RodrigoChe/fonte_de_bancada/cad_mecanico/COMPONENTES/sapata.SLDPRT

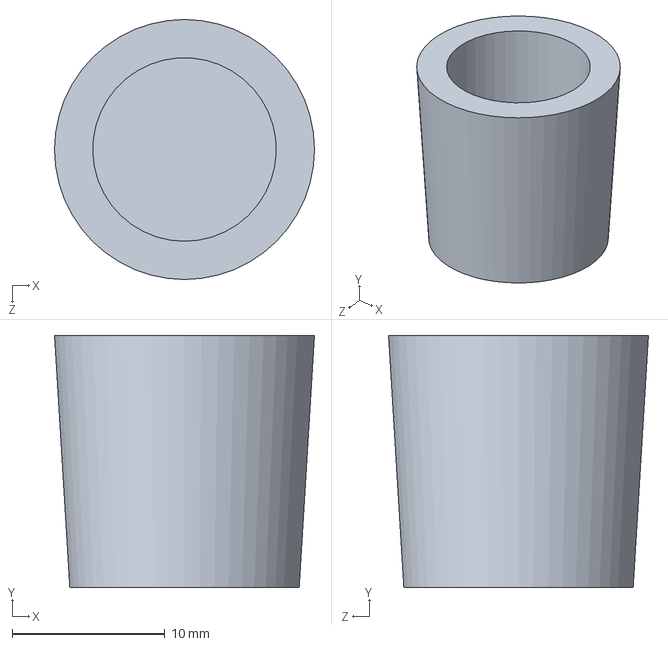
[picture p17: CAD file, 2024-03-11]
cad_mecanico/COMPONENTES/sapata.SLDPRT
17.0 x 16.5 x 17.0 mm
