RodrigoChe/fonte_de_bancada/cad_mecanico/COMPONENTES/trafo 3A.SLDPRT

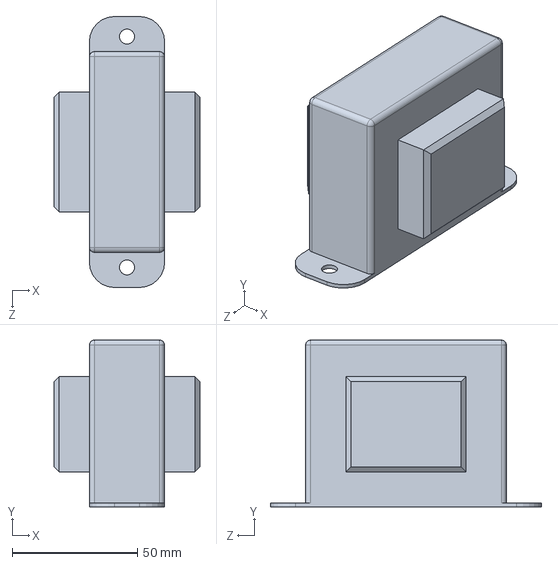
[picture p18: CAD file, 2024-03-11]
cad_mecanico/COMPONENTES/trafo 3A.SLDPRT
58.0 x 66.5 x 108.0 mm
