RodrigoChe/fonte_de_bancada/cad_mecanico/COMPONENTES/Chave HH.SLDPRT

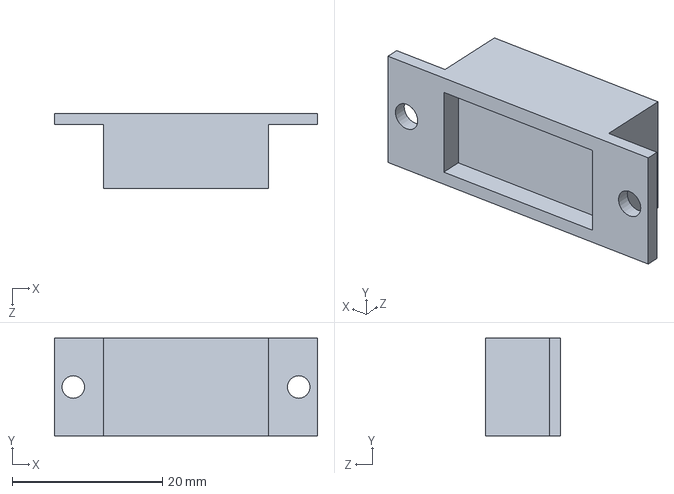
[picture p19: CAD file, 2024-03-11]
cad_mecanico/COMPONENTES/Chave HH.SLDPRT
35.0 x 13.0 x 10.0 mm
