RodrigoChe/fonte_de_bancada/cad_mecanico/COMPONENTES/Orelha.SLDPRT

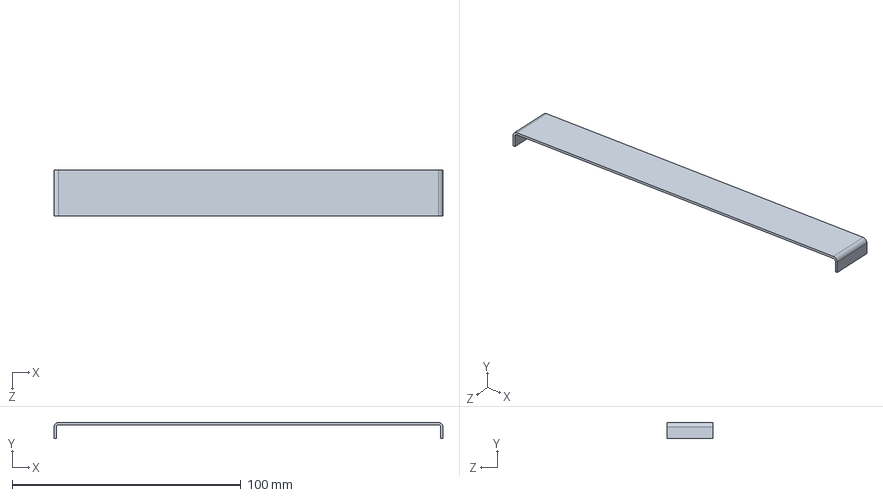
[picture p20: CAD file, 2024-03-11]
cad_mecanico/COMPONENTES/Orelha.SLDPRT
170.0 x 7.00 x 20.0 mm
