RodrigoChe/fonte_de_bancada/cad_mecanico/COMPONENTES/Frontal.SLDPRT

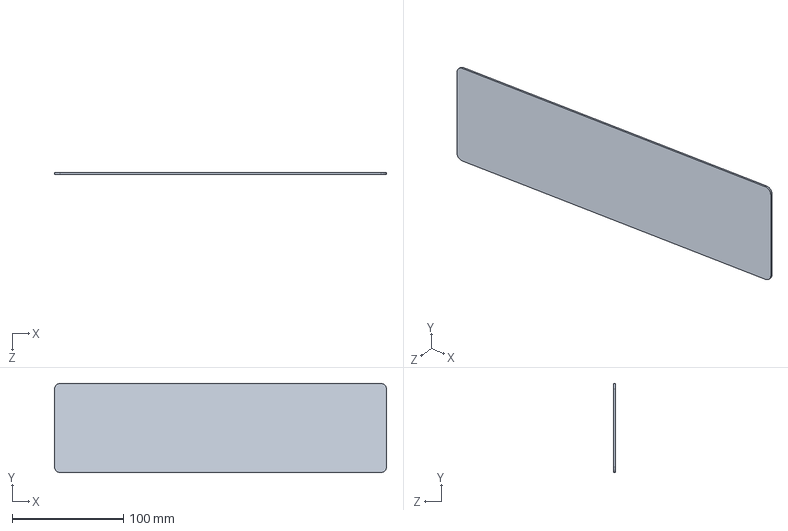
[picture p21: CAD file, 2024-03-11]
cad_mecanico/COMPONENTES/Frontal.SLDPRT
298.0 x 80.0 x 1.50 mm
