RodrigoChe/fonte_de_bancada/cad_mecanico/COMPONENTES/led holder.SLDPRT

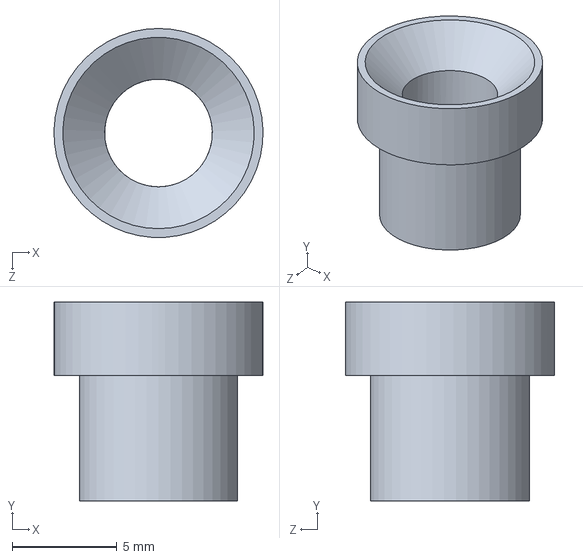
[picture p22: CAD file, 2024-03-11]
cad_mecanico/COMPONENTES/led holder.SLDPRT
9.99 x 9.50 x 10.0 mm
