RodrigoChe/fonte_de_bancada/prints_fotos_videos/cad_vista_monategm_1.png

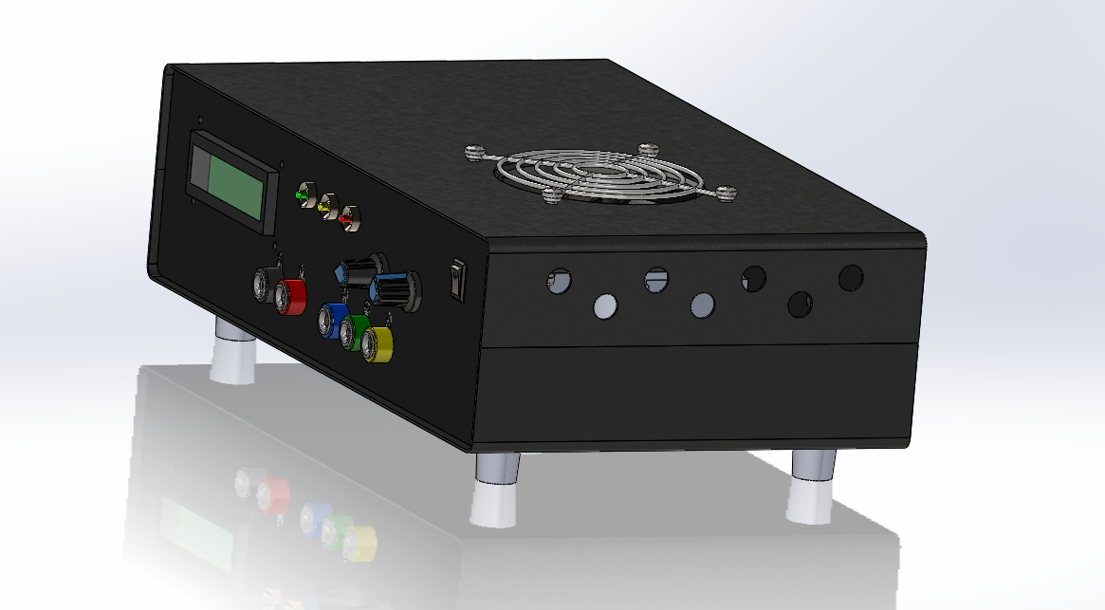
prints_fotos_videos/cad_vista_monategm_1.png
