RodrigoChe/fonte_de_bancada/prints_fotos_videos/cad_vista_monategm_2.png

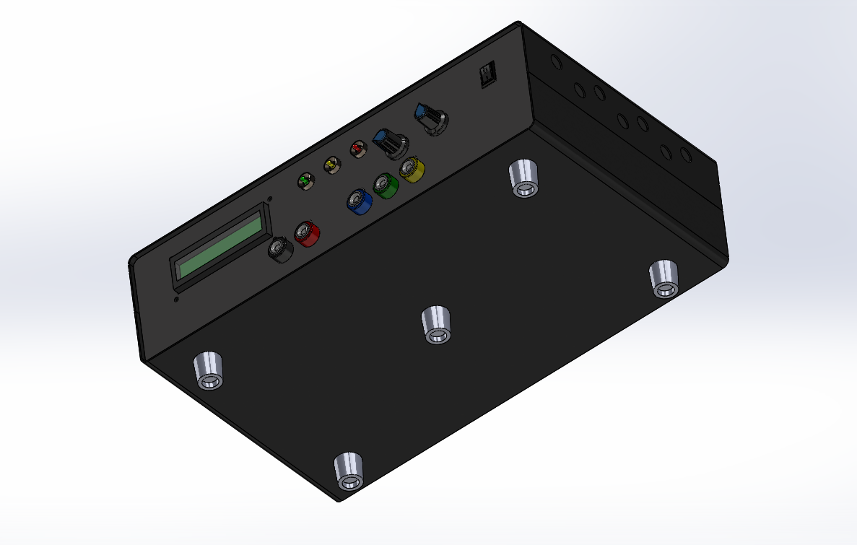
prints_fotos_videos/cad_vista_monategm_2.png
