RodrigoChe/fonte_de_bancada/prints_fotos_videos/IMG-20220224-WA0000.jpg

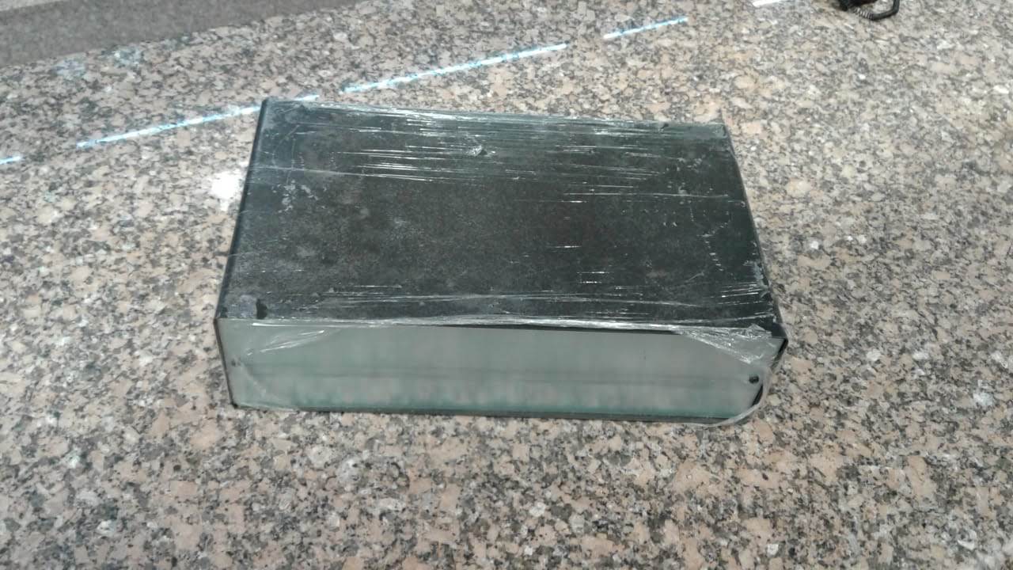
prints_fotos_videos/IMG-20220224-WA0000.jpg
