RodrigoChe/fonte_de_bancada/prints_fotos_videos/IMG-20240229-WA0002.jpeg

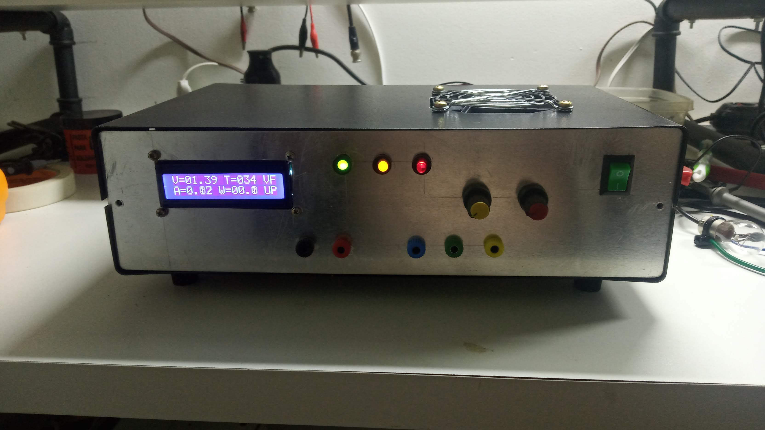
prints_fotos_videos/IMG-20240229-WA0002.jpeg
