RodrigoChe/fonte_de_bancada/prints_fotos_videos/IMG-20240301-WA0006.jpeg

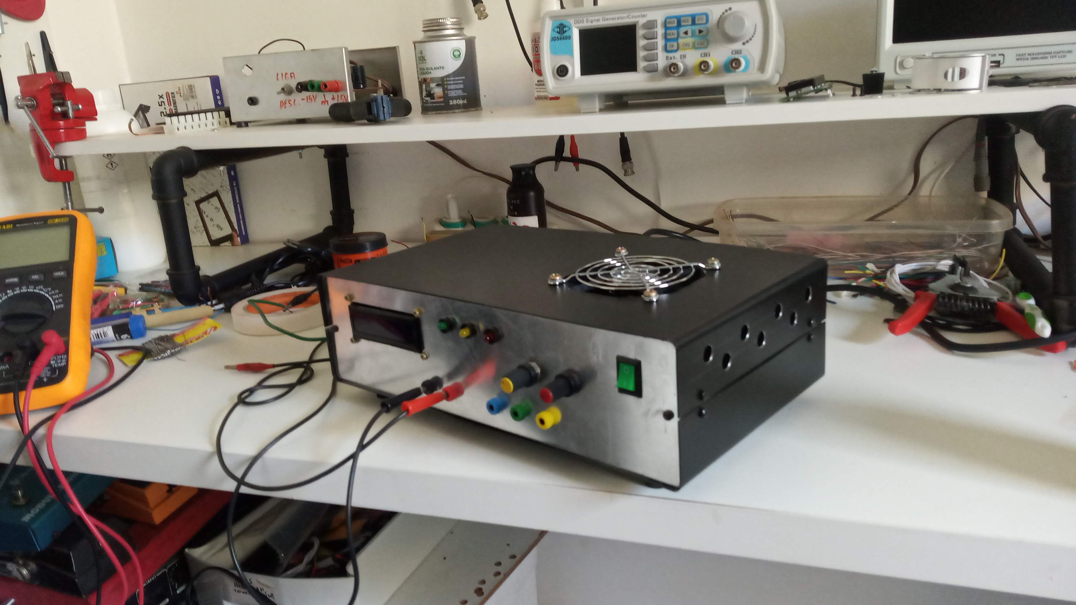
prints_fotos_videos/IMG-20240301-WA0006.jpeg
