RodrigoChe/fonte_de_bancada/prints_fotos_videos/IMG_20220310_143831.jpg

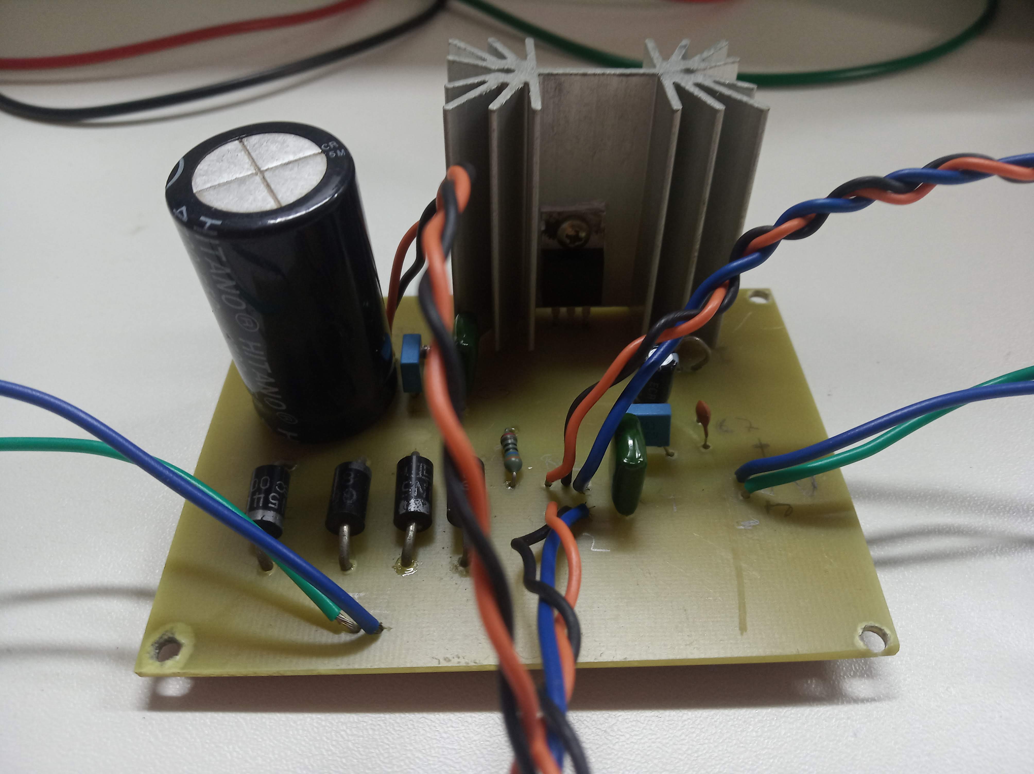
prints_fotos_videos/IMG_20220310_143831.jpg
