RodrigoChe/fonte_de_bancada/prints_fotos_videos/IMG_20220315_130520.jpg

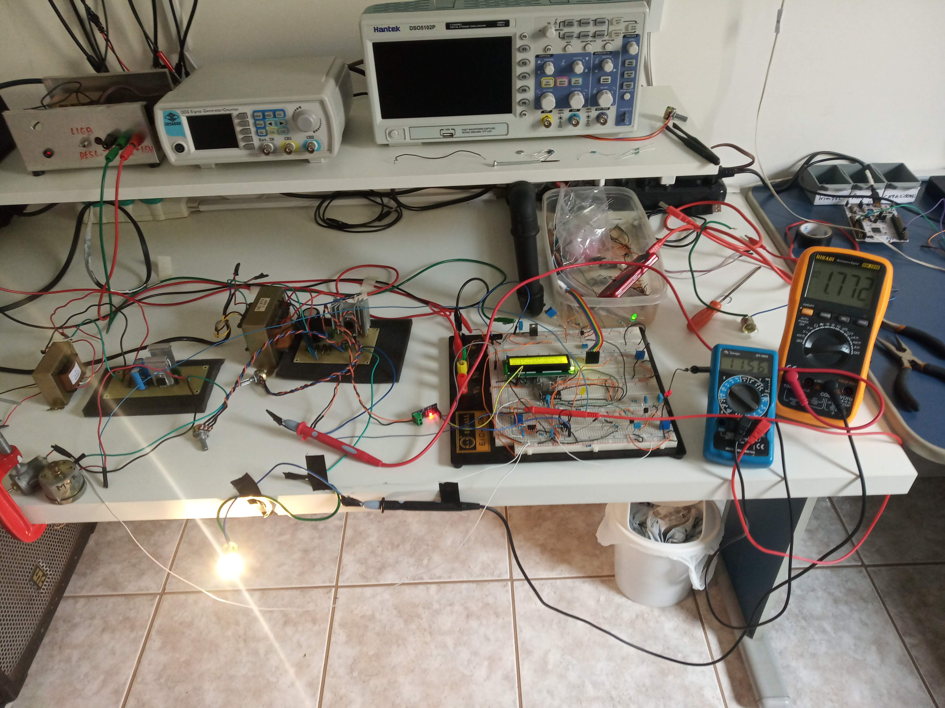
prints_fotos_videos/IMG_20220315_130520.jpg
