RodrigoChe/fonte_de_bancada/prints_fotos_videos/IMG_20231120_121806.jpg

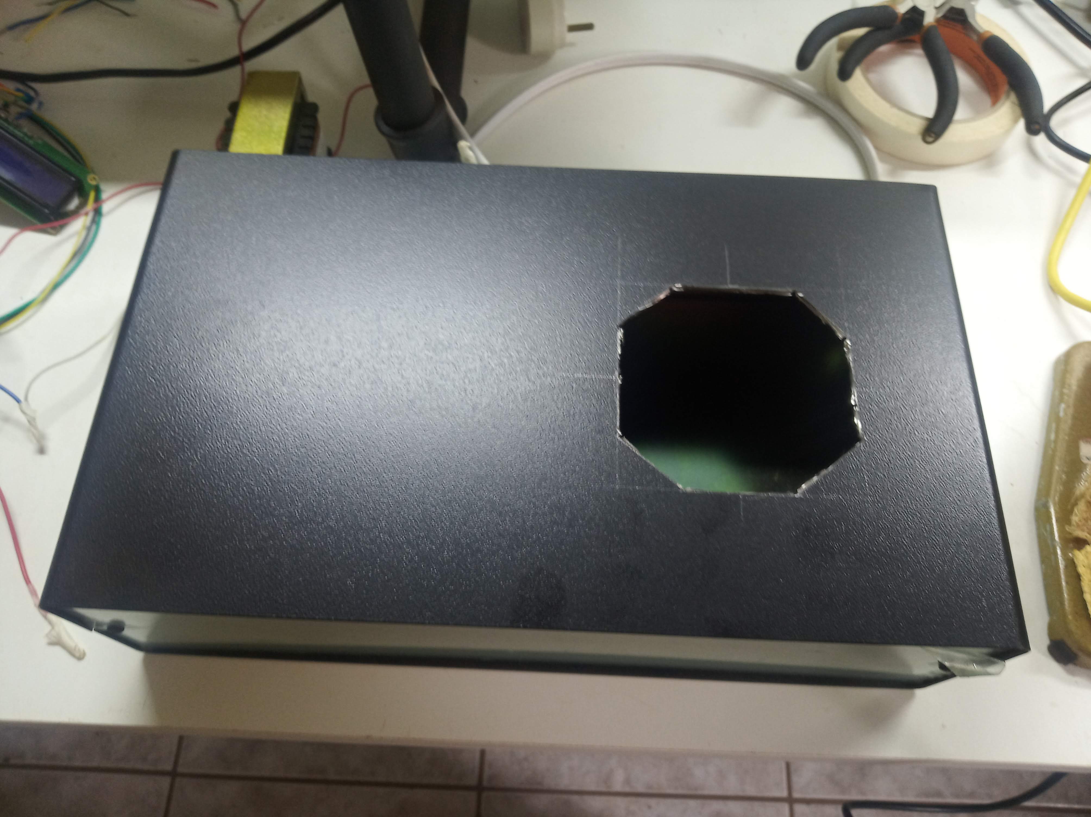
prints_fotos_videos/IMG_20231120_121806.jpg
