RodrigoChe/fonte_de_bancada/prints_fotos_videos/IMG_20231228_160359.jpg

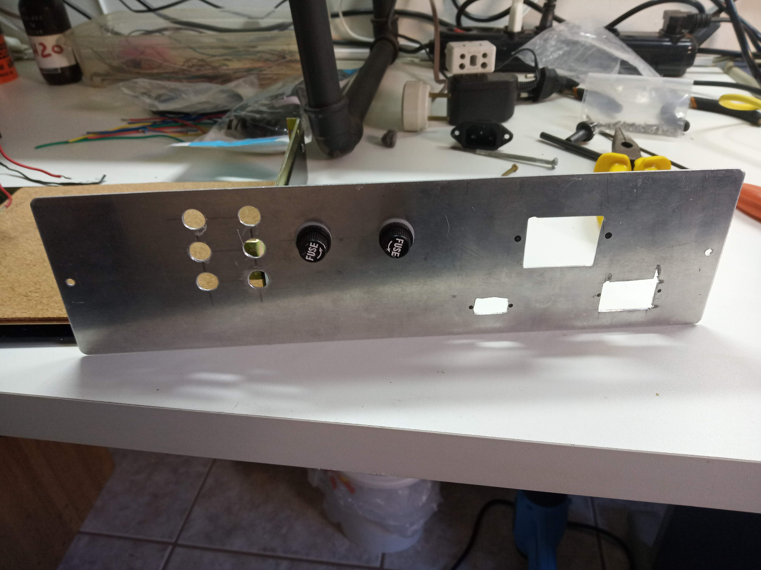
prints_fotos_videos/IMG_20231228_160359.jpg
