RodrigoChe/fonte_de_bancada/prints_fotos_videos/IMG_20231229_150956.jpg

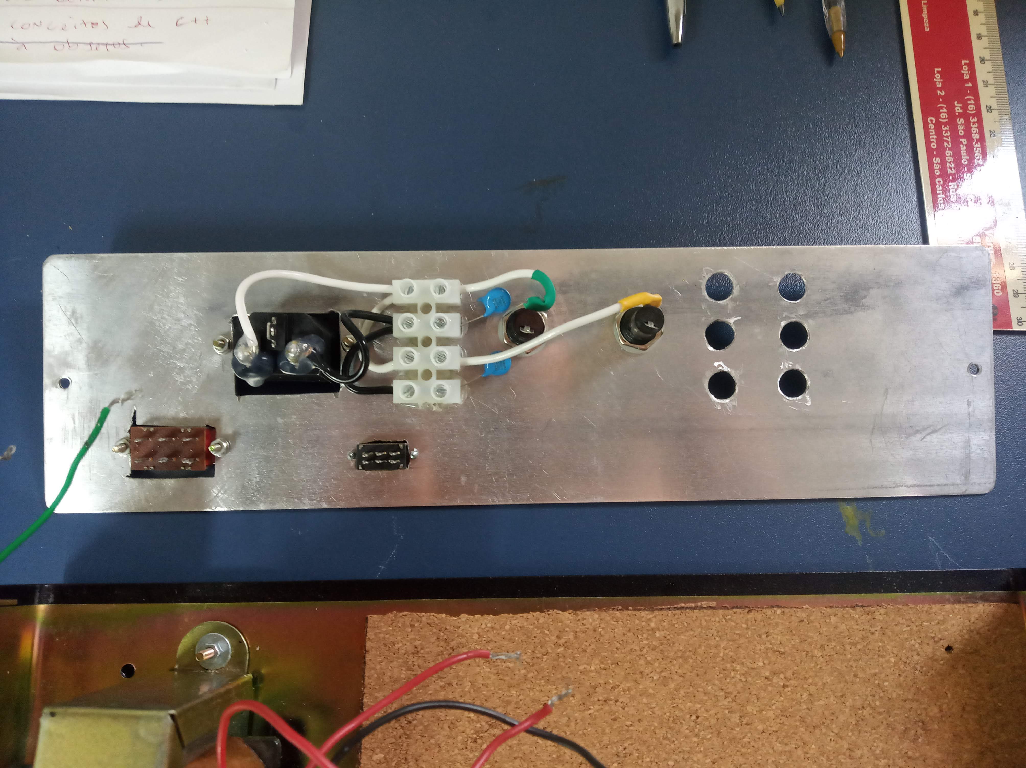
prints_fotos_videos/IMG_20231229_150956.jpg
