RodrigoChe/fonte_de_bancada/prints_fotos_videos/IMG_20240110_225814.jpg

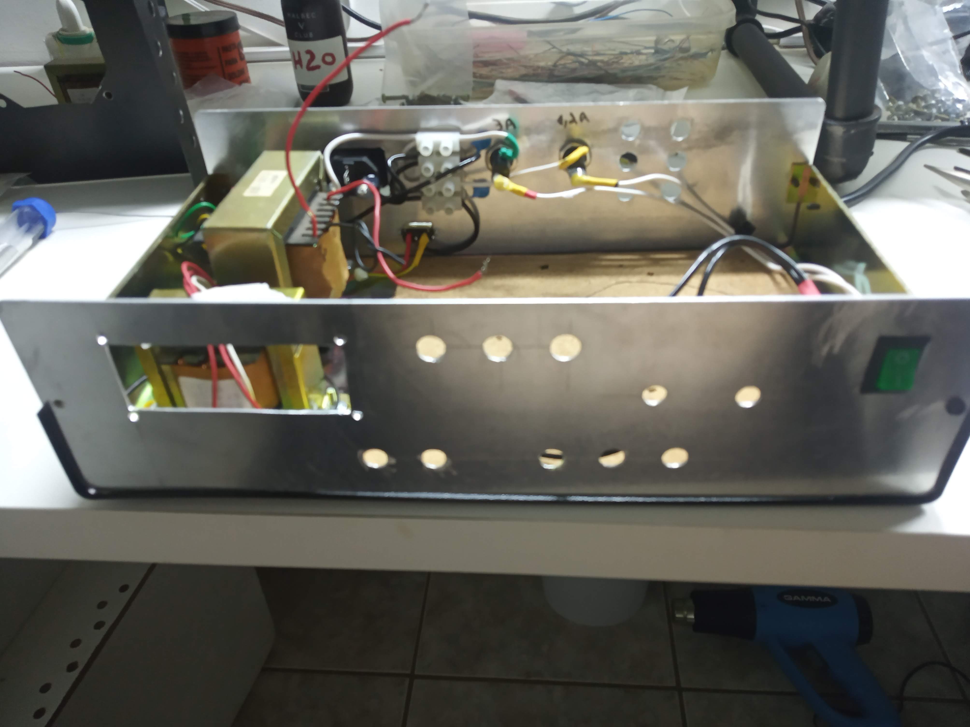
prints_fotos_videos/IMG_20240110_225814.jpg
