RodrigoChe/fonte_de_bancada/prints_fotos_videos/IMG_20240113_201511.jpg

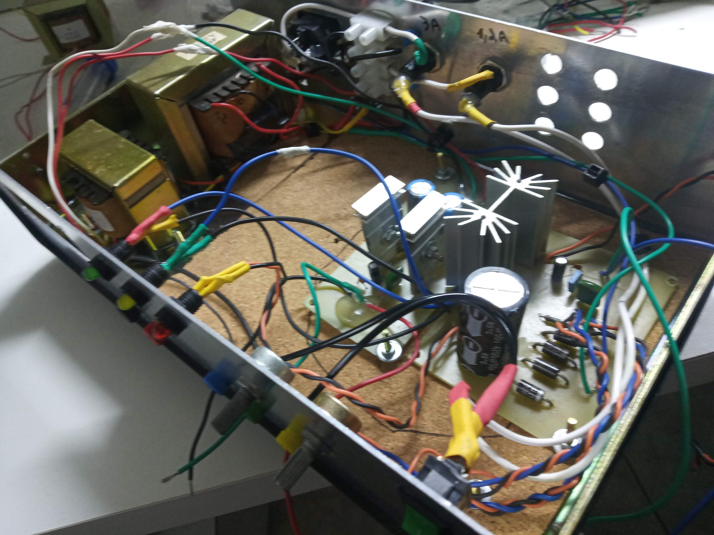
prints_fotos_videos/IMG_20240113_201511.jpg
