RodrigoChe/fonte_de_bancada/prints_fotos_videos/IMG_20240210_154214.jpg

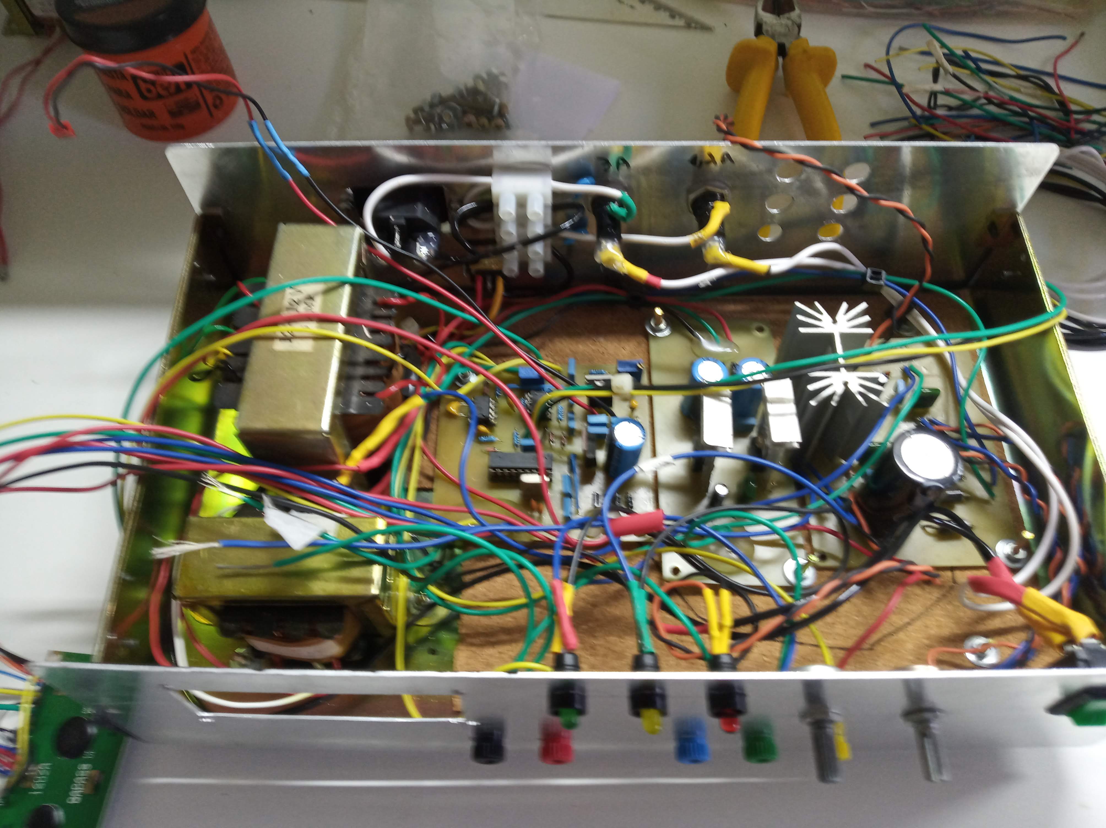
prints_fotos_videos/IMG_20240210_154214.jpg
