RodrigoChe/fonte_de_bancada/prints_fotos_videos/simula.PNG

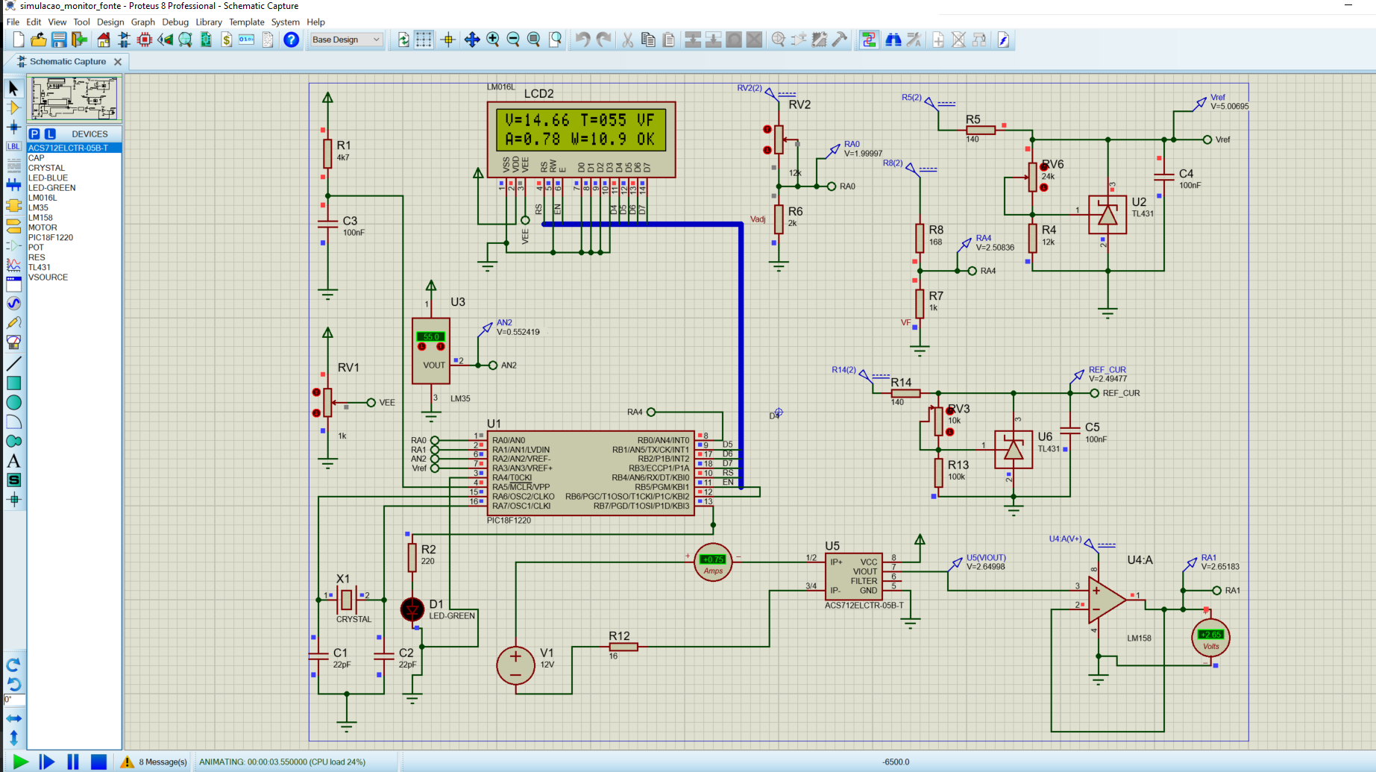
prints_fotos_videos/simula.PNG
