RodrigoChe/fonte_de_bancada/fontes/esquematicos_placas/fonte_simetrica.pdsprj.pdf

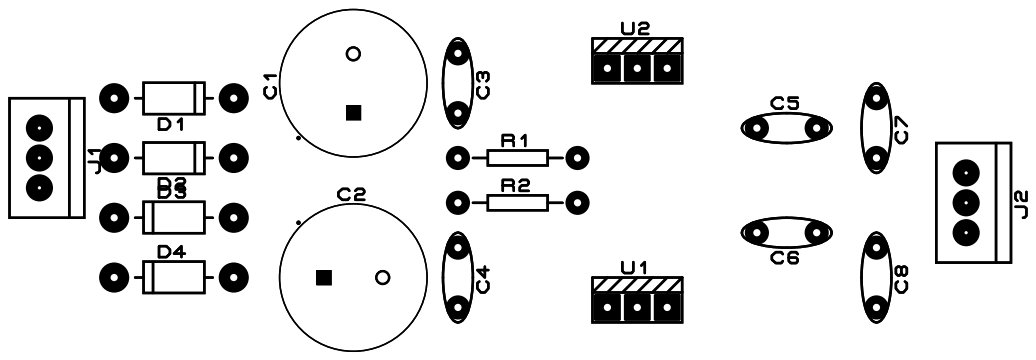
[picture p62: page 1]
