RodrigoChe/fonte_de_bancada/fontes/esquematicos_placas/fonte_simetrica_esquema.pdsprj.pdf

U2

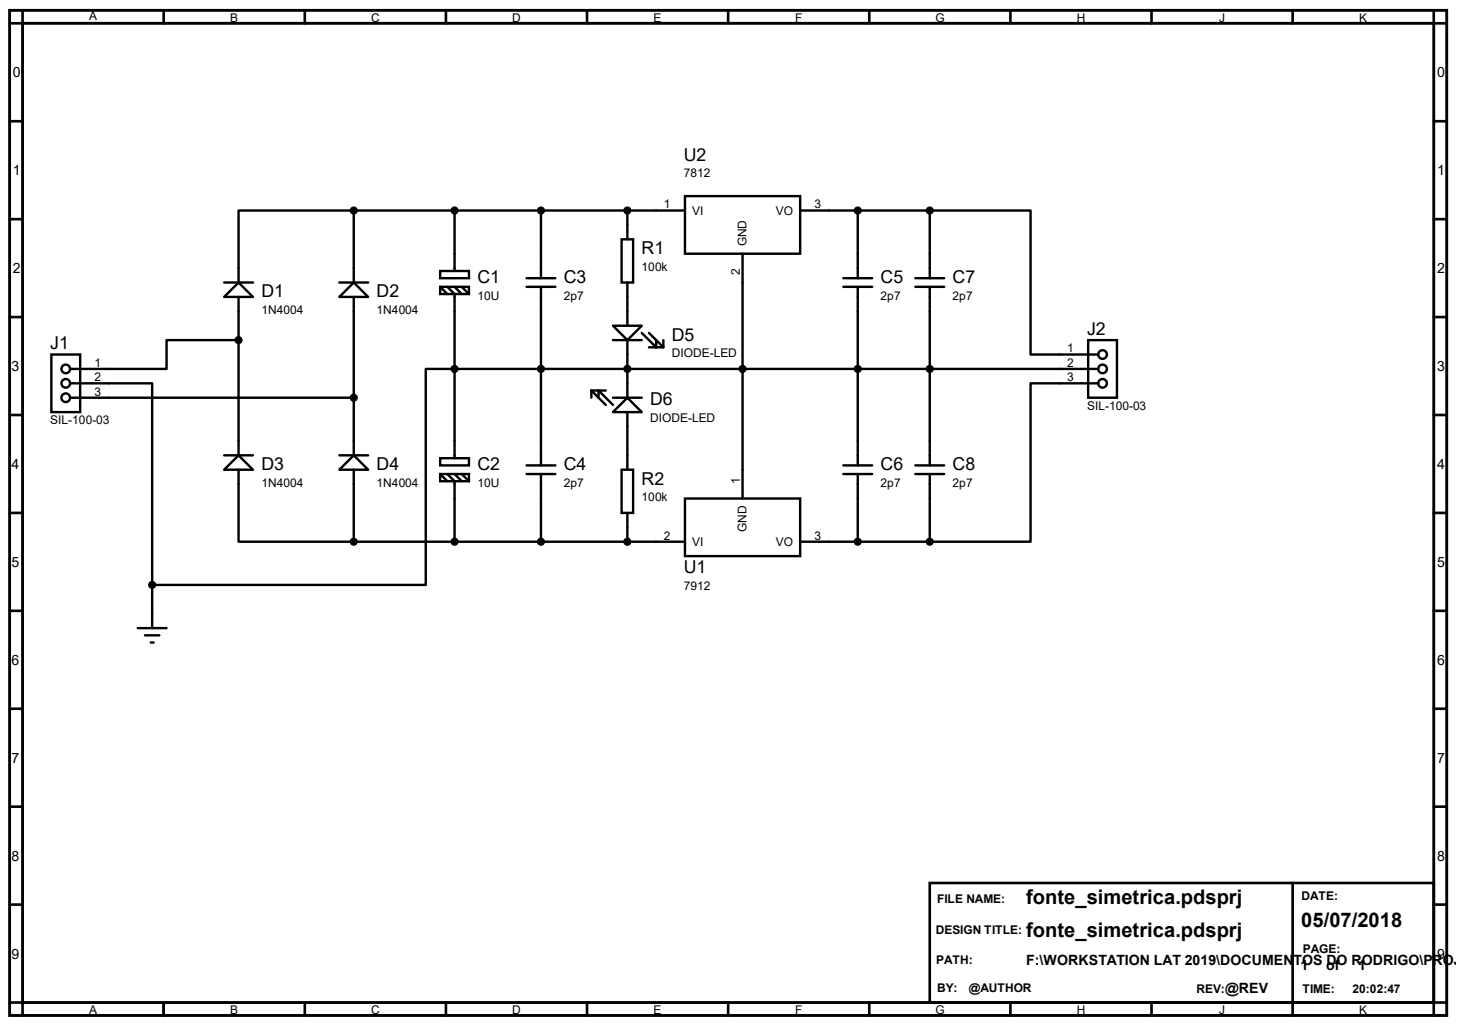
[picture p63: page 1]
