RodrigoChe/fonte_de_bancada/fontes/esquematicos_placas/fonte_variavel.pdsprj.pdf

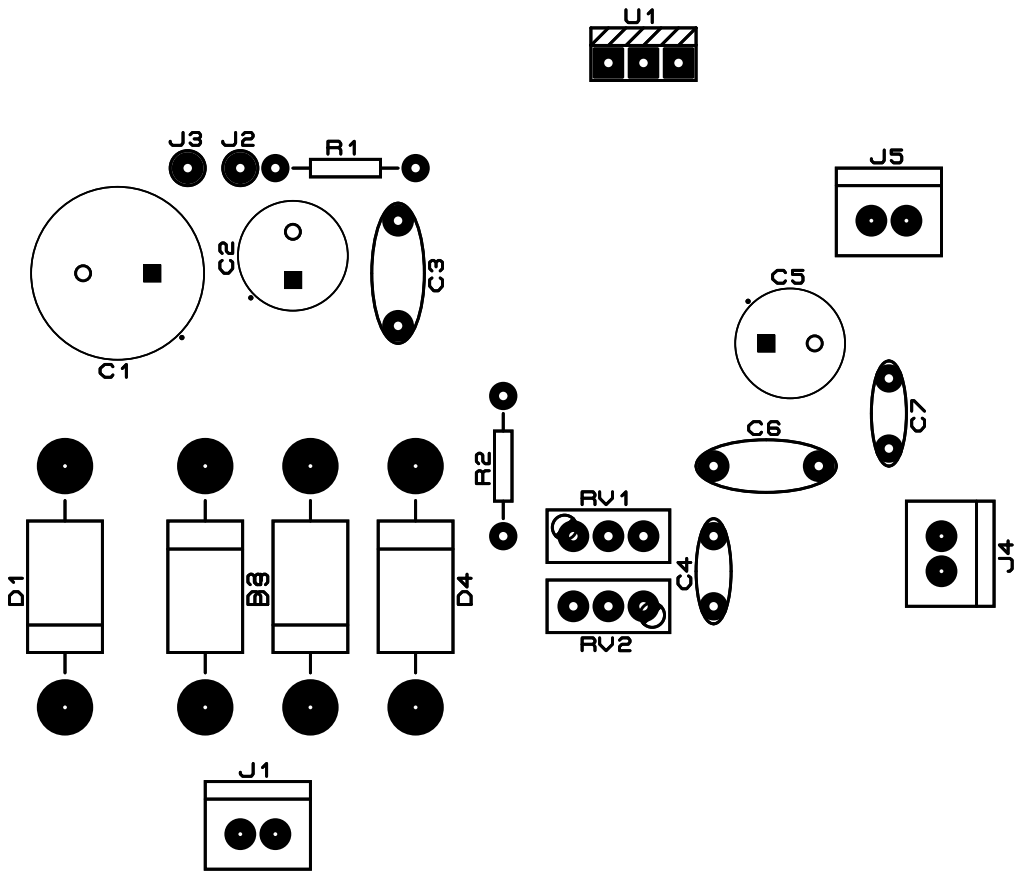
[picture p64: page 1]
