RodrigoChe/fonte_de_bancada/fontes/esquematicos_placas/fonte_variavel_esquema.pdsprj.pdf

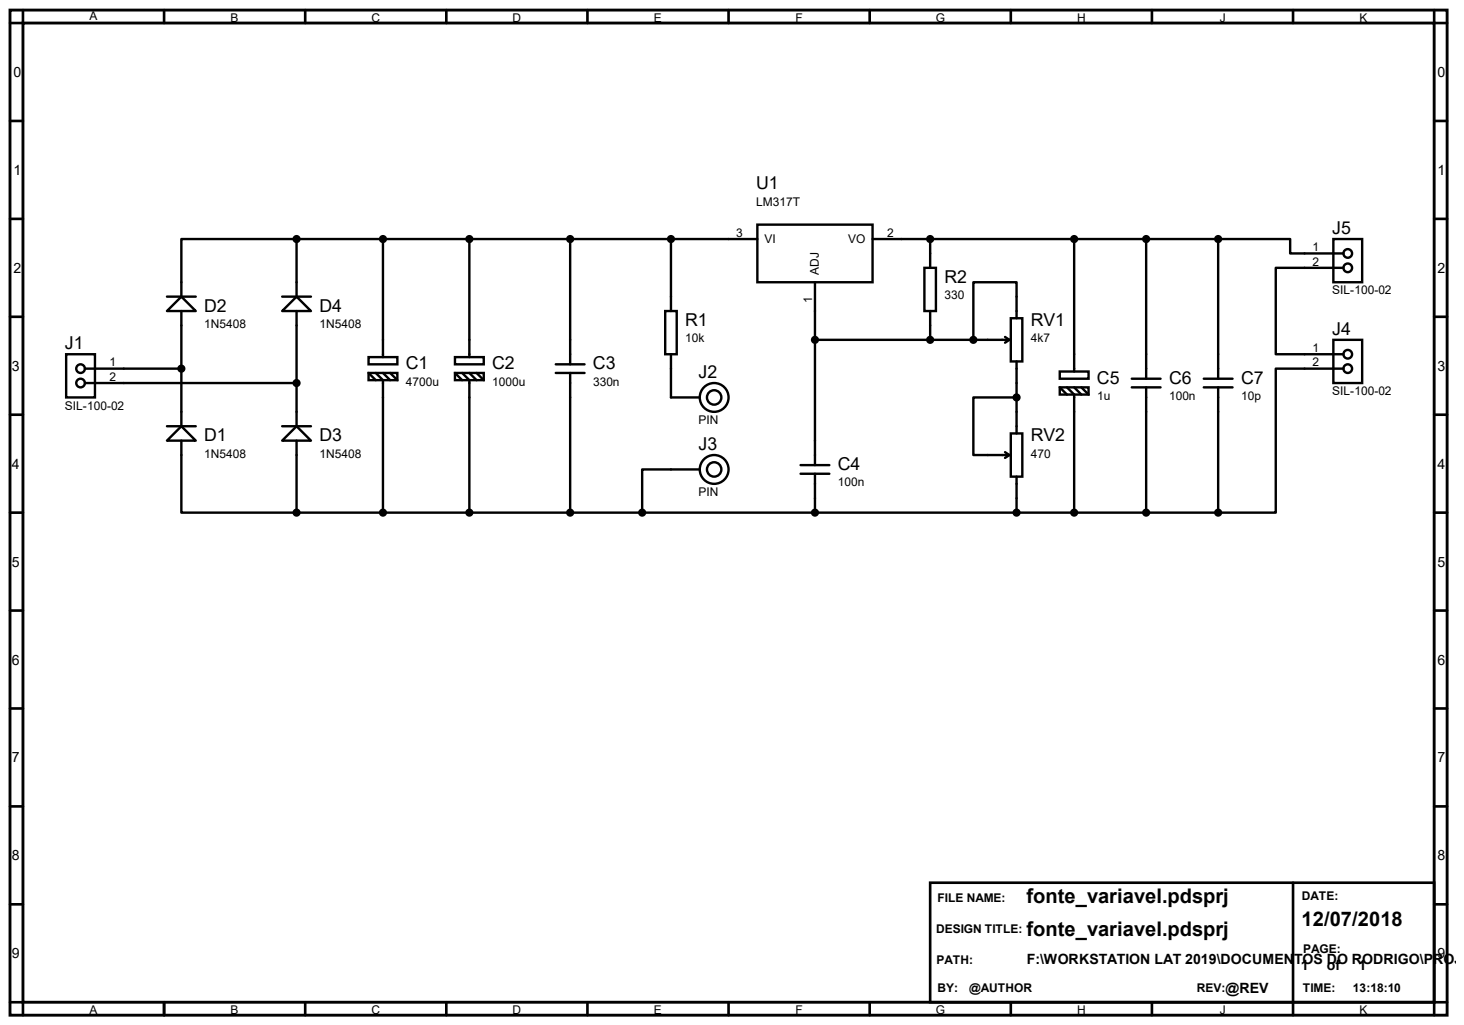
[picture p65: page 1]
