RodrigoChe/fonte_de_bancada/monitor_fonte/PCB_Altium/PCB_INSTRUMENTATION_VSOURCE/Producao/Thermal_transfer/Mask_Impressao_TermoCAM.pdf

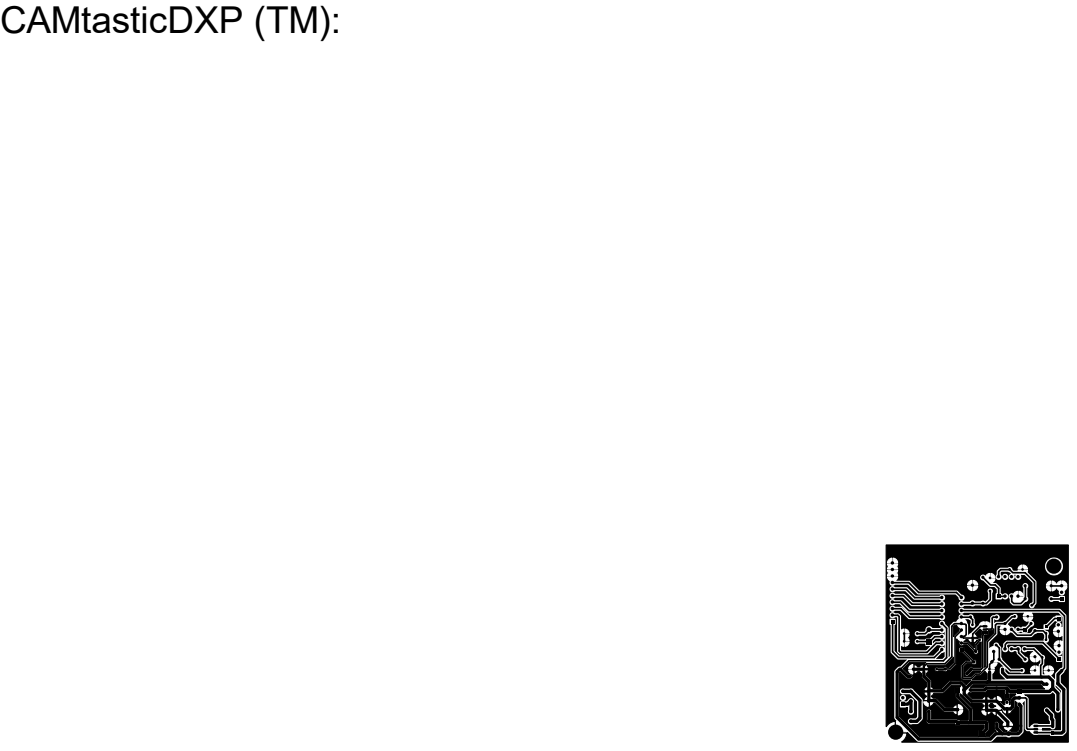
[picture p66: page 1]
CAMtasticDXP (TM):
