RodrigoChe/fonte_de_bancada/monitor_fonte/Firmware/firmware_monitor.c

/****************************************************************
* @file : firmware_monitor.c
*
*
*****************************************************************/

/* Includes */
#include "Device.h"

void main(){

 Device_init();
  
  while(1) {                         // Endless loop
    Device_run();
  }
}
